danbrick92/r2d2/print/real/v1/lazy_susan_body.stl

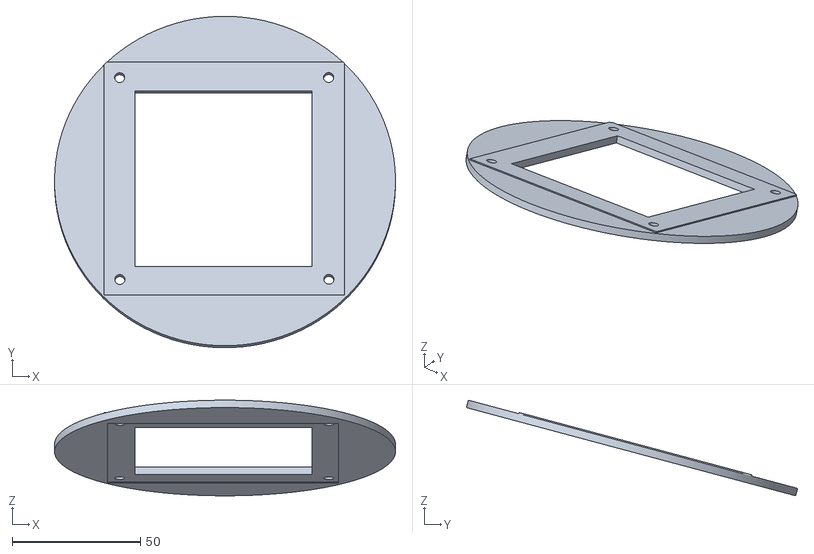
[picture p16: CAD file, 2025-09-23]
print/real/v1/lazy_susan_body.stl
133.0 x 129.2 x 37.3
