danbrick92/r2d2/print/real/v1/left_foot.stl

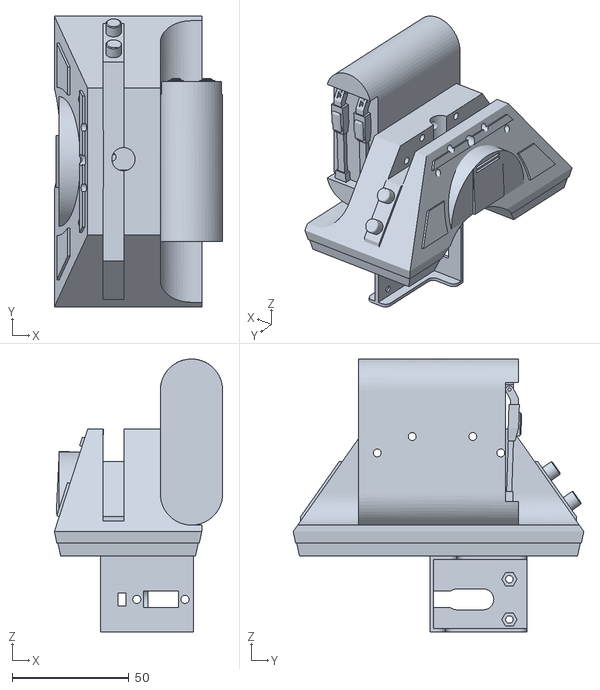
[picture p17: CAD file, 2025-09-19]
print/real/v1/left_foot.stl
72.2 x 124.7 x 117.1
