danbrick92/r2d2/print/real/v1/right_foot.stl

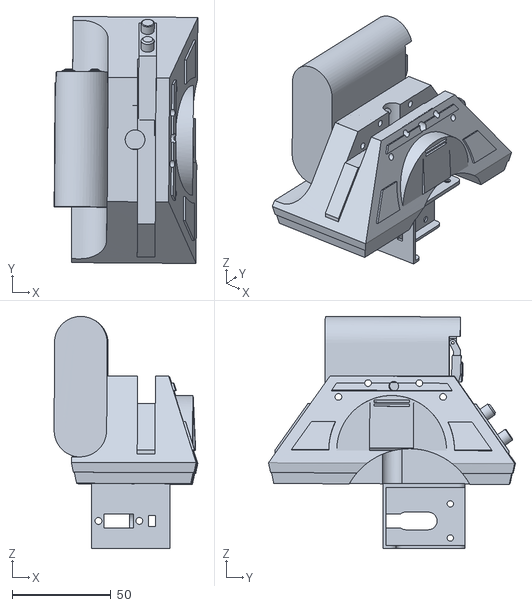
[picture p18: CAD file, 2025-09-19]
print/real/v1/right_foot.stl
72.8 x 125.2 x 117.6
