danbrick92/r2d2/print/real/v1/right_leg.stl

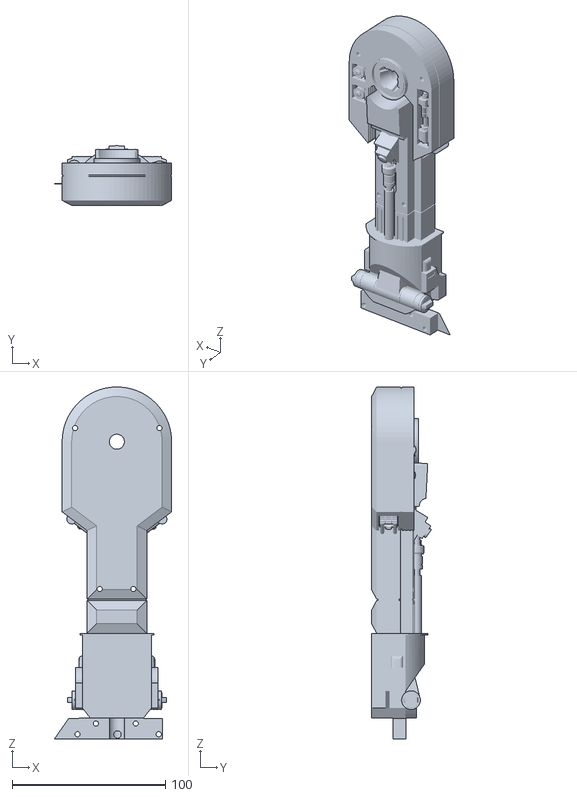
[picture p19: CAD file, 2025-09-19]
print/real/v1/right_leg.stl
76.6 x 39.1 x 229.8
