danbrick92/r2d2/print/real/v1/left_leg.stl

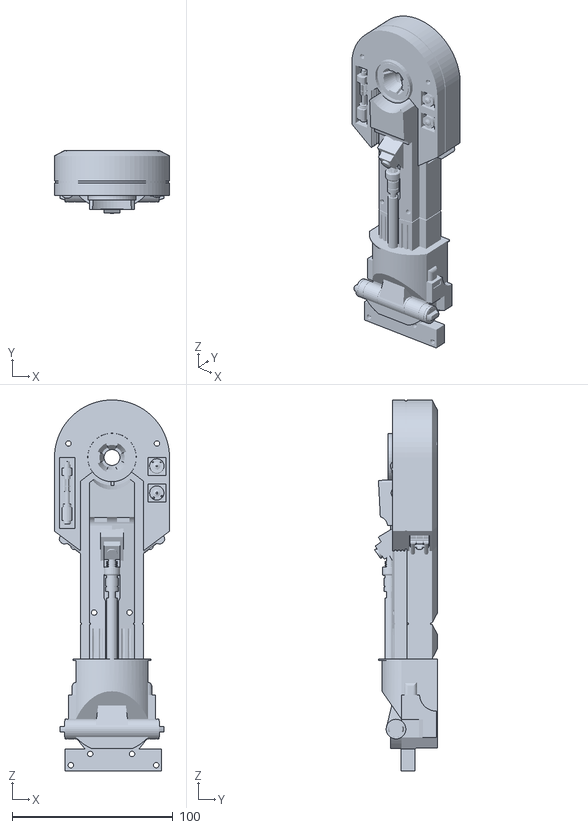
[picture p20: CAD file, 2025-09-19]
print/real/v1/left_leg.stl
71.5 x 39.1 x 230.5
