danbrick92/r2d2/print/test/motorMount/images/IMG_20160407_083758.jpg

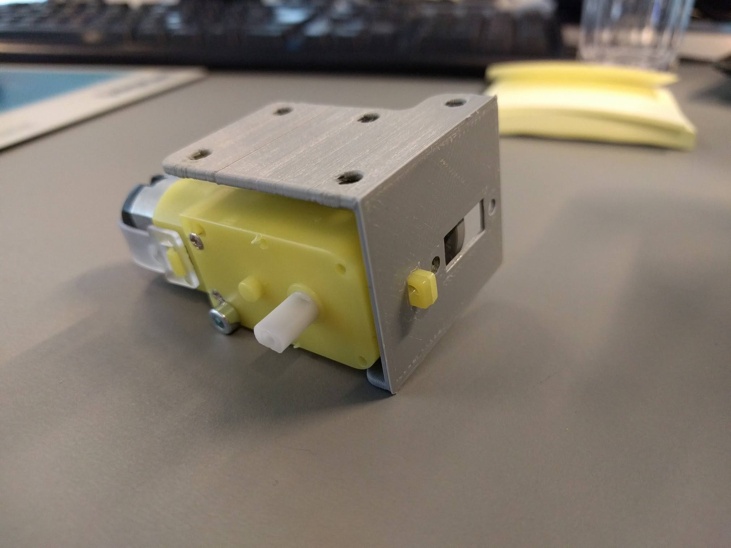
print/test/motorMount/images/IMG_20160407_083758.jpg
