danbrick92/r2d2/print/test/motorMount/images/IMG_20160407_083924.jpg

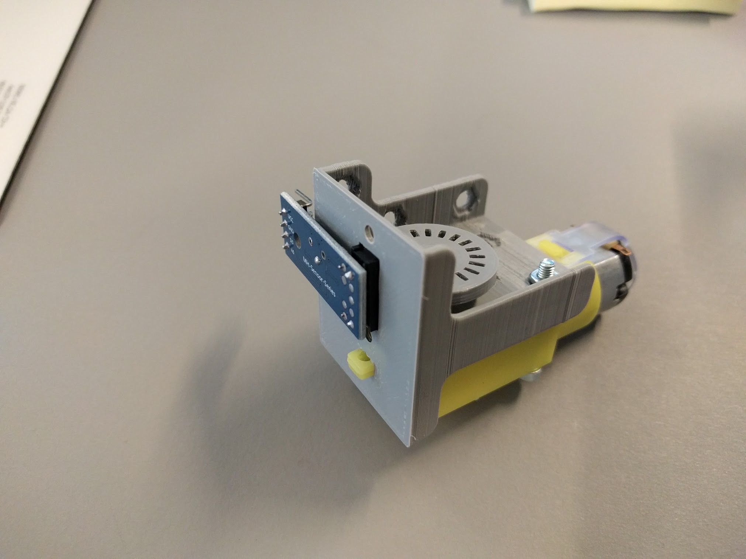
print/test/motorMount/images/IMG_20160407_083924.jpg
